ZuhayrHalday/EEE4022S-CR3D-Final_Thesis_Project/Analog Front-End Subsystem/LTSpice Simulations/AFE_Sim.asc

C1: cap; 22pF
C2: cap; 330pF
C5: cap; 22pF
C6: cap; 220nF
C7: cap; 3pF
D1: schottky; BAT54
OPA365: UniversalOpAmp2; Avol=1e5 GBW=50Meg Slew=25Meg; Ilimit=30m Rail=0 Vos=0.2m
OPA656: UniversalOpAmp2; Avol=1e5 GBW=230Meg Slew=290Meg; Ilimit=30m Rail=0 Vos=0
R1: res; 1k
R2: res; 5k
R5: res; 5.6k
R6: res; 470
V1: voltage; PULSE(0 5 10ms 0 0 1us 10ms)
V2: voltage; 4.7
Named nets: 0, V+, V_Out, V_TIA_Out
.param Q1pe=1.17p
.param Npe=1
.param Q=100*{Npe*Q1pe}
.param tau_r=1n tau_f=55n t0=5m
.param T=10m
.tran 0 50m 4ms 50n startup
